af-3/Oil-Spill-Active-Radar-Target-ECE-510/Team_One_Design/LTspice/555timer_simulation.asc

C1: cap; 1n
C2: cap; .01µ
R1: res; 100k
R2: res; 14.43k
U1: NE555
V1: voltage; 1
Named nets: 0, VDD, Vdd, X, OUT
.tran 0 .0001 0 .000001
